c3lingo/c3lingo-interpreter-unit/schematics/c3lingo_unit-assembly/kicad-libraries/c3lingo_unit-3dmodels/Potentiometer_Alps_RK09K_Single_Horizontal.step

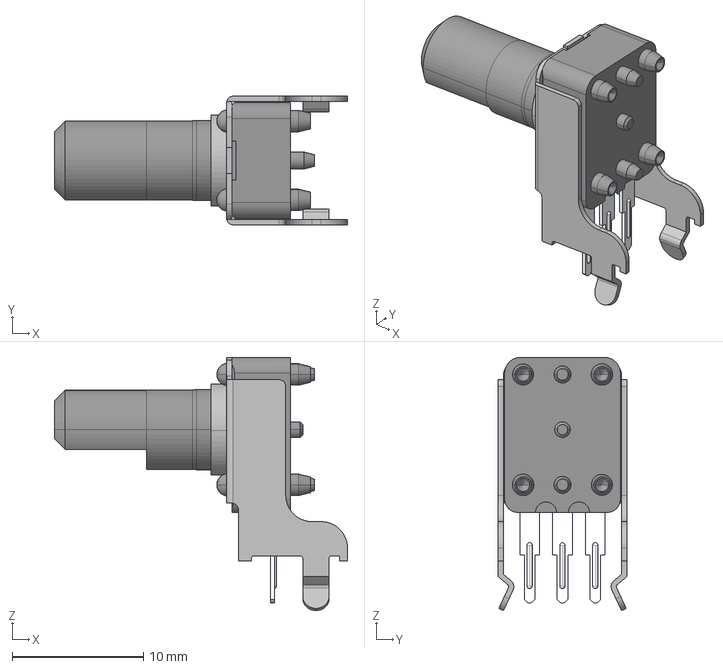
[picture p17: CAD file, 2025-08-26]
schematics/c3lingo_unit-assembly/kicad-libraries/c3lingo_unit-3dmodels/Potentiometer_Alps_RK09K_Single_Horizontal.step
22.3 x 9.80 x 19.3 mm
