c3lingo/c3lingo-interpreter-unit/schematics/c3lingo_unit-assembly/kicad-libraries/c3lingo_unit-3dmodels/TerminalBlock_Phoenix_SPTAF-1-4-3.5_1x04.step

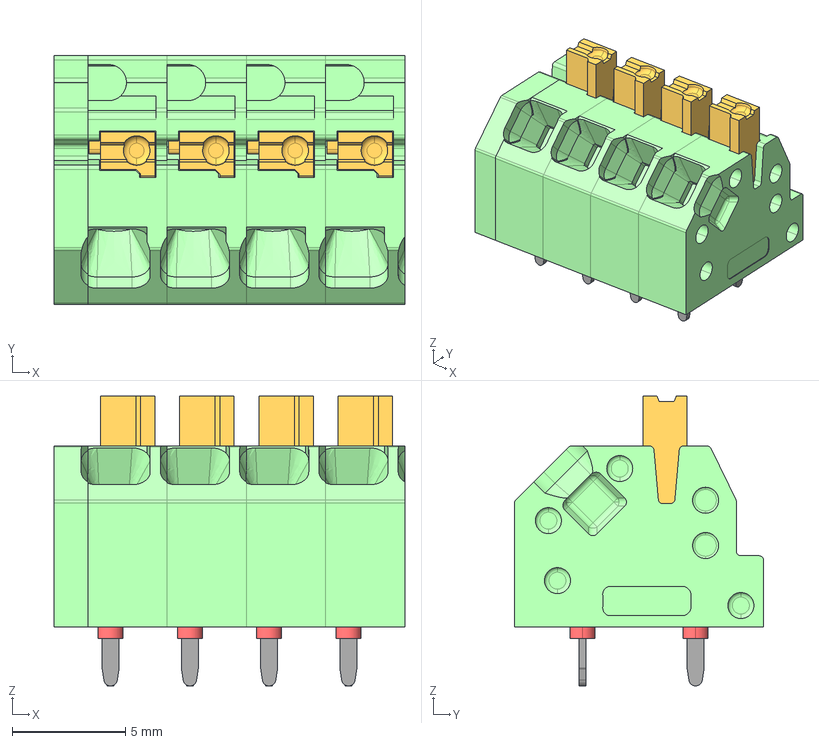
[picture p18: CAD file, 2025-08-26]
schematics/c3lingo_unit-assembly/kicad-libraries/c3lingo_unit-3dmodels/TerminalBlock_Phoenix_SPTAF-1-4-3.5_1x04.step
15.5 x 11.0 x 12.8 mm
Bohrloch.1.1 x 4
Bohrloch.2 x 4
SPTAF_1-3.5_housing x 4
SPTAF-0-DKL.1
