c3lingo/c3lingo-interpreter-unit/schematics/mixer/c3lingo-interpreter-unit.sch

## KiCad design schematics/mixer/c3lingo-interpreter-unit.sch (2021-04-18)

Schematic: c3lingo-interpreter-unit.sch

Parts:
C1, C9, C19, C21, C23: 100uF; CP_Radial_D10.0mm_P5.00mm
C2, C4, C5, C8, C11, C12, C15, C16, C22, C25: 100nF; C_Disc_D5.0mm_W2.5mm_P5.00mm
C3, C10: 22pF; C_Disc_D5.0mm_W2.5mm_P5.00mm
C6, C7, C13, C20: 1uF; CP_Radial_D5.0mm_P2.00mm
C14: 47pF; C_Disc_D5.0mm_W2.5mm_P5.00mm
C17, C18: 1uF; C_Disc_D5.0mm_W2.5mm_P5.00mm
C24: 220uF; CP_Radial_D6.3mm_P2.50mm
C26: 47nF; C_Disc_D5.0mm_W2.5mm_P5.00mm
C27: 220pF; C_Disc_D5.0mm_W2.5mm_P5.00mm
D1, D2, D3, D4: 1N4148; D_DO-35_SOD27_P10.16mm_Horizontal
J1: Headphone 1; PinHeader_1x04_P2.54mm_Vertical
J2: Mic 1; PinHeader_1x04_P2.54mm_Vertical
J3: Mix Line-Out; PinHeader_1x04_P2.54mm_Vertical
J4: Stage Line-In; PinHeader_1x04_P2.54mm_Vertical
J5, J6: PowerSupply; TerminalBlock_MetzConnect_Type073_RT02603HBLU_1x03_P5.08mm_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
R1, R10: 1K 1%; R_Axial_DIN0207_L6.3mm_D2.5mm_P10.16mm_Horizontal
R2, R11: 330K 1%; R_Axial_DIN0207_L6.3mm_D2.5mm_P10.16mm_Horizontal
R3, R8, R17, R18, R21, R23: 10K; R_Axial_DIN0207_L6.3mm_D2.5mm_P10.16mm_Horizontal
R4: 3.3K; R_Axial_DIN0207_L6.3mm_D2.5mm_P10.16mm_Horizontal
R5: 27K 1%; R_Axial_DIN0207_L6.3mm_D2.5mm_P10.16mm_Horizontal
R6: 1.5K; R_Axial_DIN0207_L6.3mm_D2.5mm_P10.16mm_Horizontal
R7: 470R; R_Axial_DIN0207_L6.3mm_D2.5mm_P10.16mm_Horizontal
R9, R12, R13, R14, R16, R19, R28, R29, R30, R31: 22K; R_Axial_DIN0207_L6.3mm_D2.5mm_P10.16mm_Horizontal
R15, R22: 680R 1%; R_Axial_DIN0207_L6.3mm_D2.5mm_P10.16mm_Horizontal
R20: 47K; R_Axial_DIN0207_L6.3mm_D2.5mm_P10.16mm_Horizontal
R24: 330K; R_Axial_DIN0207_L6.3mm_D2.5mm_P10.16mm_Horizontal
R25: 12R; R_Axial_DIN0207_L6.3mm_D2.5mm_P10.16mm_Horizontal
R26: 270R; R_Axial_DIN0207_L6.3mm_D2.5mm_P10.16mm_Horizontal
R27: 2.2K; R_Axial_DIN0207_L6.3mm_D2.5mm_P10.16mm_Horizontal
RV1: 100K; Potentiometer_Vishay_T73XX_Horizontal
RV11, RV13, RV14, RV19: 50K log.; Potentiometer_Alps_RK11K_Single_Horizontal
RV15: 50K log. st.; Potentiometer_Alps_RK09L_Double_Horizontal
SW1: Mute_1; PinHeader_1x02_P2.54mm_Vertical
SW2: OnAir_1; PinHeader_1x04_P2.54mm_Vertical
TP1, TP3, TP9: Mic1; TestPoint_THTPad_D2.0mm_Drill1.0mm
TP2, TP8: Stage; TestPoint_THTPad_D2.0mm_Drill1.0mm
TP4, TP10: Mic2; TestPoint_THTPad_D2.0mm_Drill1.0mm
TP5, TP11: Mic3; TestPoint_THTPad_D2.0mm_Drill1.0mm
TP6: MicSum; TestPoint_THTPad_D2.0mm_Drill1.0mm
U1, U3, U4: LM833N; DIP-8_W7.62mm_Socket_LongPads
U2: NE5534; DIP-8_W7.62mm_Socket_LongPads
U5: DRV134PA; DIP-8_W7.62mm_Socket_LongPads
U7: LM386N-4; DIP-8_W7.62mm_Socket_LongPads

Notes on the sheet:
Mic Preamp Gain: 50 dB
Adjustable Input Gain Gain: -15 to 30 dB
Input Module Gain: -6 to +8 dB Gain = (R_pot + R_22k) / R_47k LP_filter(R_pot): 130 - 22 kHz
Headphone driver Gain: 26 dB (20)
TODO: On-Air button LEDs (actually one rd, one gn, with common anode)
HP Filter 350 Hz f_c = 1/(2*PI*R*C)
Balanced Line Input Converter Gain: 1 220pF for HF rolloff (20 kHz)
TODO: C at pin 7 has no audible effect
Mic3
Mic2
Summing Module Gain: -inf to 0 dB per Ch.
Line driver Gain: 6 dB
Summing Module Gain: 0 dB
Phantom Power (15V)
